Kitware/adapt/docs/img/adapt_white.png

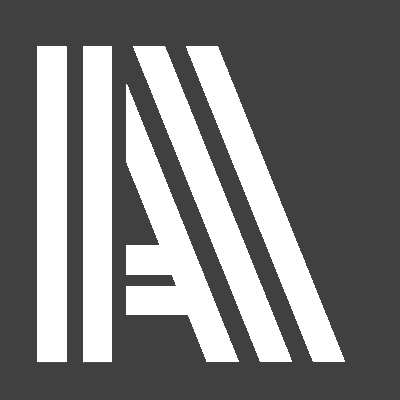
docs/img/adapt_white.png
