Kitware/adapt/docs/img/bridge2.png

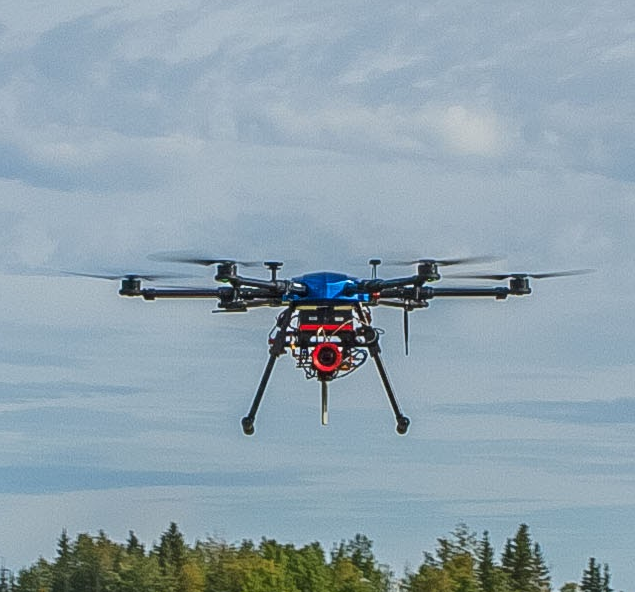
docs/img/bridge2.png
