Kitware/adapt/docs/img/cb1.jpg

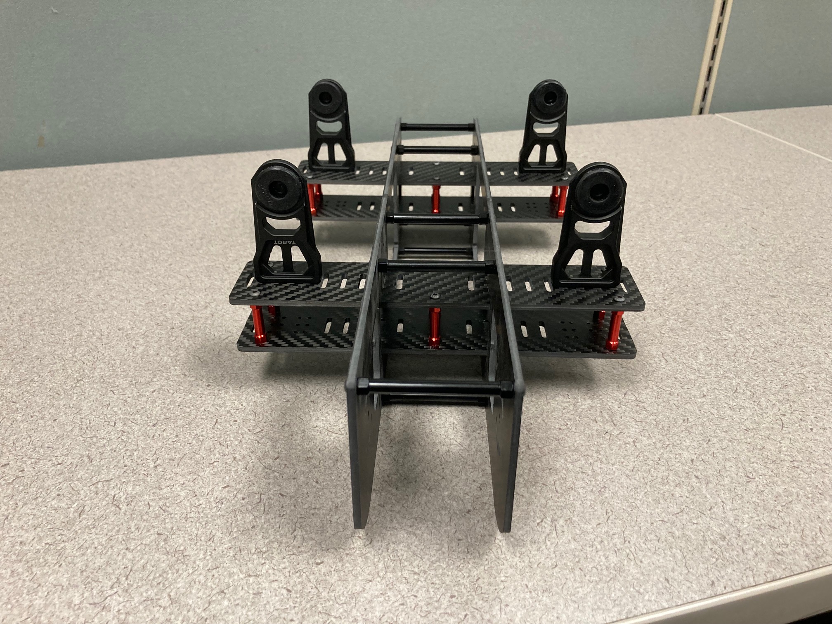
docs/img/cb1.jpg
